rusefi/proteus-Honda-OBD2A-adapter/boards/proteusOBD2Ahonda-test/board/misc/proteusOBD2Ahonda-test-bottom.png

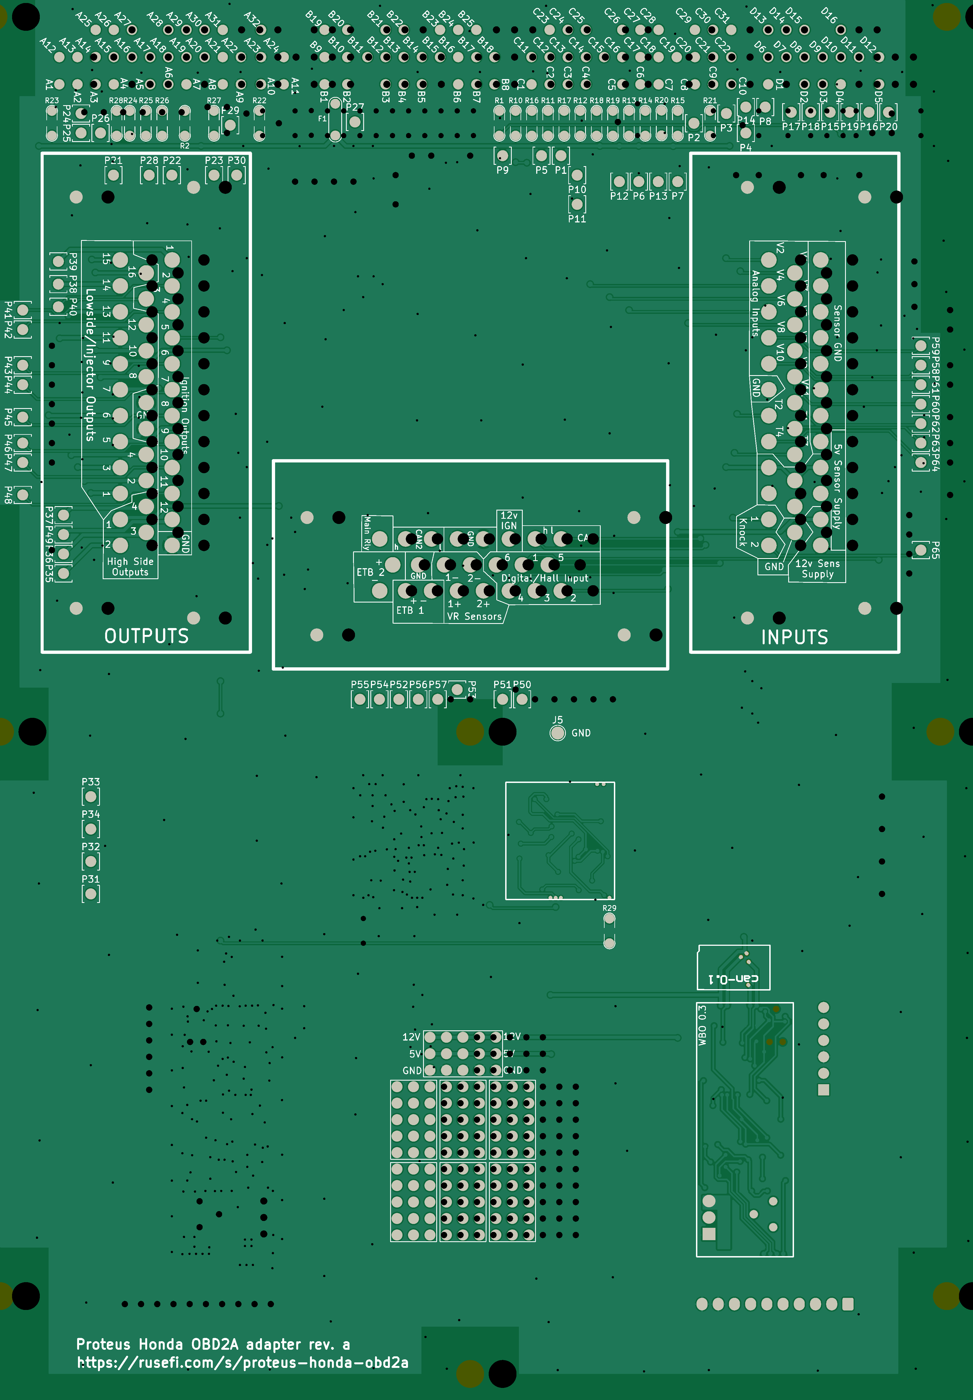
boards/proteusOBD2Ahonda-test/board/misc/proteusOBD2Ahonda-test-bottom.png
