rusefi/proteus-Honda-OBD2A-adapter/boards/proteusOBD2Ahonda-test/board/proteusOBD2Ahonda-test.png

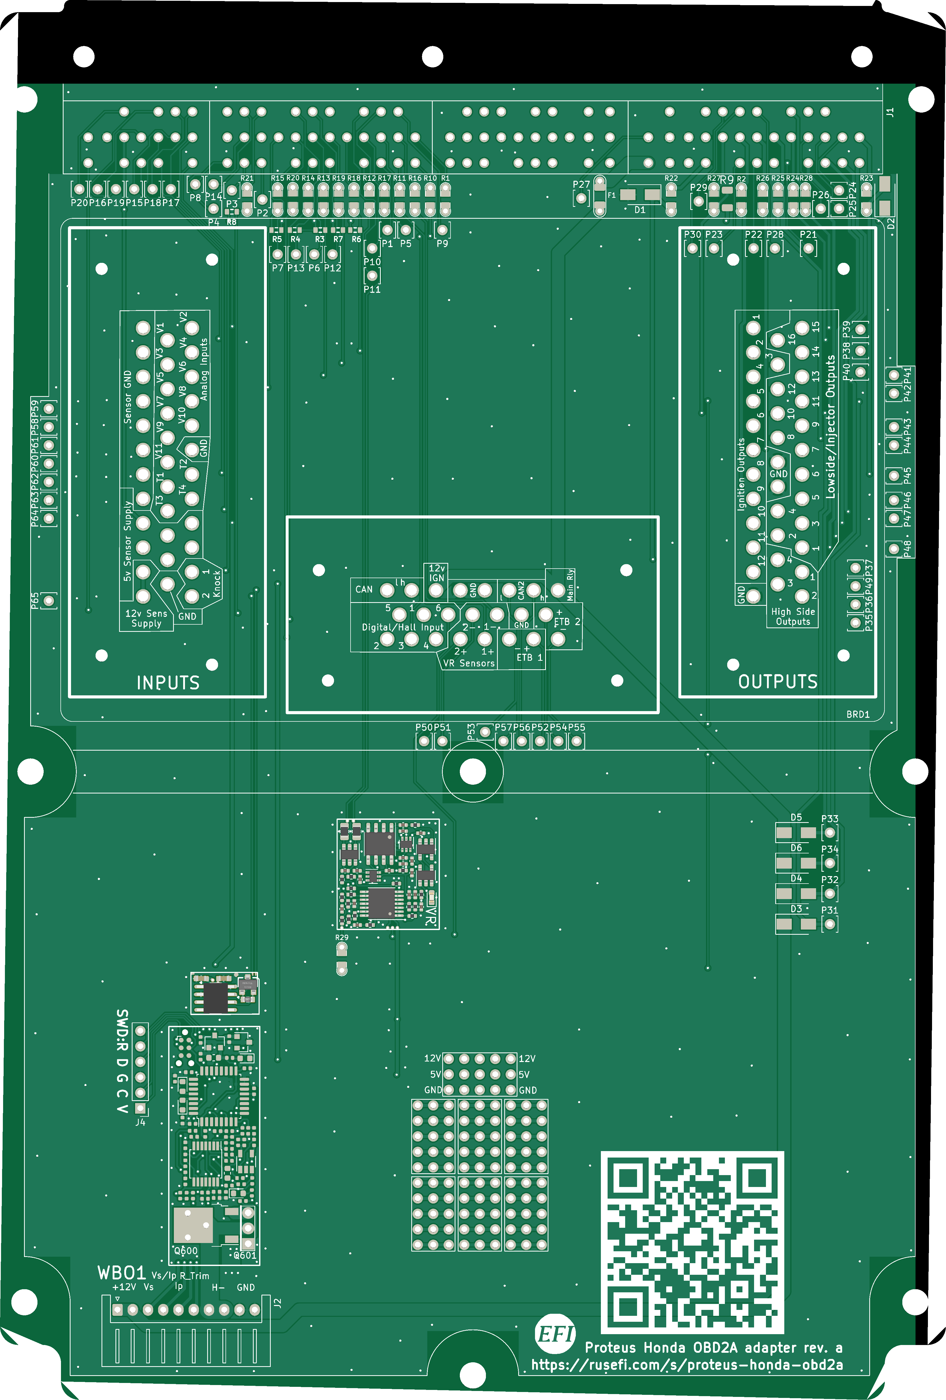
boards/proteusOBD2Ahonda-test/board/proteusOBD2Ahonda-test.png
